HeinrichG-V12/MFL/BeckerPioneerFW/BeckerPioneerFW/adc/adc.h

/*
 * adc.h
 *
 * Created: 03.01.2020 15:47:03
 *  Author: Heinrich
 */ 

#include <avr/io.h>
#include <avr/interrupt.h>
#include <stdint.h>

#ifndef ADC_H_
#define ADC_H_

void adc_init (void);

#endif /* ADC_H_ */
