HeinrichG-V12/MFL/BeckerPioneerFW/BeckerPioneerFW/radio_control/pioneer.h

/*
 * pioneer.h
 *
 * Created: 21.03.2020 10:22:28
 *  Author: Heinrich
 */



#ifndef PIONEER_H_
#define PIONEER_H_

#include <avr/io.h>
#include <stdint.h>

#include "../mcp42xxx/mcp42xxx.h"

// pioneer_2 = PB4
// is still input!

void pioneer_init (void);
void pioneer_source (void);
void pioneer_mute (void);
void pioneer_list (void);
void pioneer_next (void);
void pioneer_next_long (void);
void pioneer_previous (void);
void pioneer_previous_long (void);
void pioneer_volume_increase (void);
void pioneer_volume_decrease (void);
void pioneer_select (void);
void pioneer_mode (void);
void pioneer_send_release (void);

#endif /* PIONEER_H_ */
